dylanjacobsun/flight_Controller/Components/10nF_Cap_0603.step

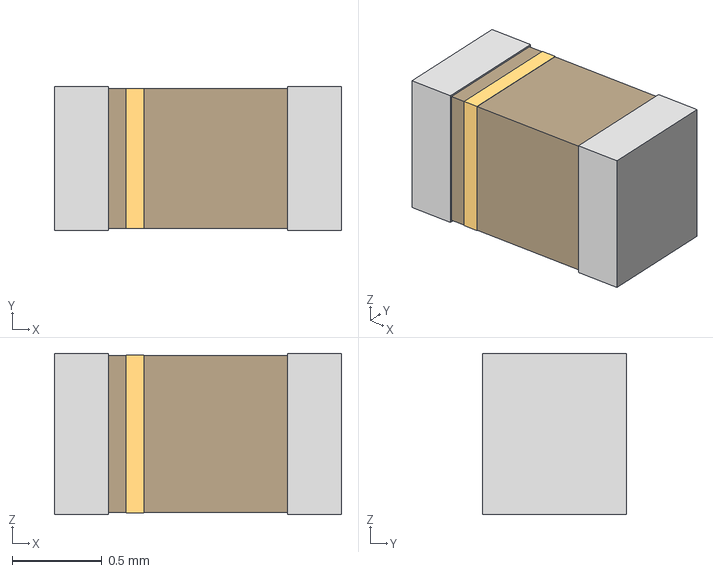
[picture p15: CAD file, 2025-04-18]
Components/10nF_Cap_0603.step
1.60 x 0.8 x 0.9 mm
