dylanjacobsun/flight_Controller/Components/33.2Resistor.step

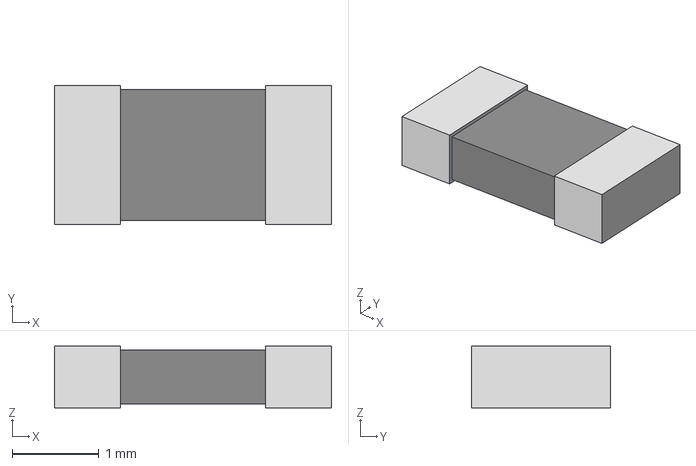
[picture p16: CAD file, 2025-04-17]
Components/33.2Resistor.step
3.20 x 1.60 x 0.711 mm
