dylanjacobsun/flight_Controller/Components/22Uf_CAP.step

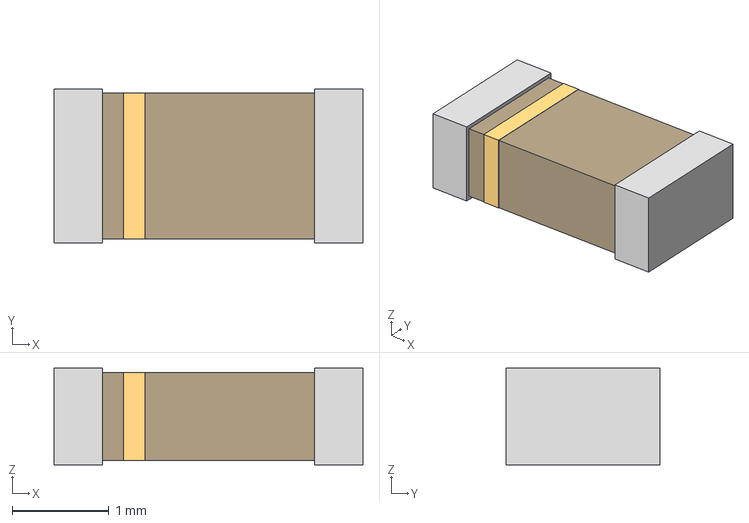
[picture p17: CAD file, 2025-04-17]
Components/22Uf_CAP.step
3.20 x 1.60 x 1.00 mm
