dylanjacobsun/flight_Controller/Components/3_3_Inductor.step

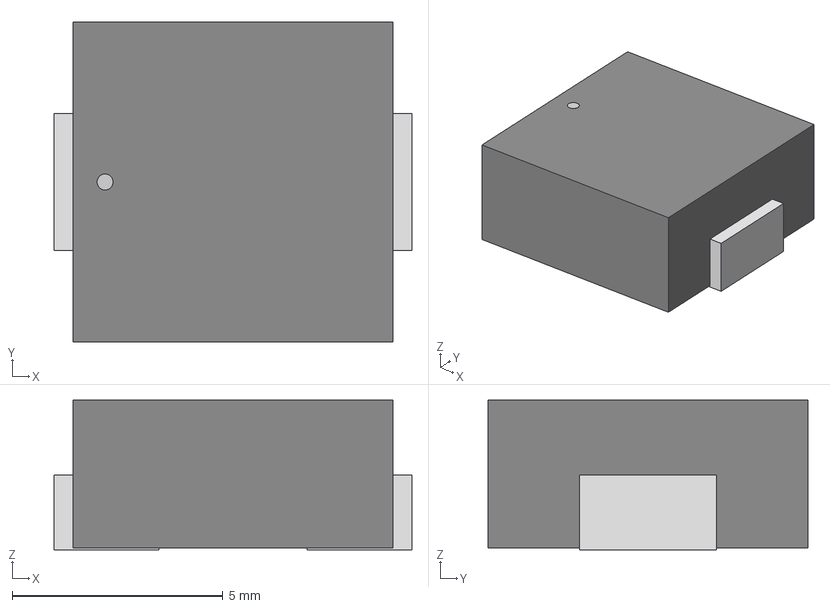
[picture p18: CAD file, 2025-04-17]
Components/3_3_Inductor.step
8.50 x 7.59 x 3.56 mm
