dylanjacobsun/flight_Controller/Components/STM32F446VET6.step

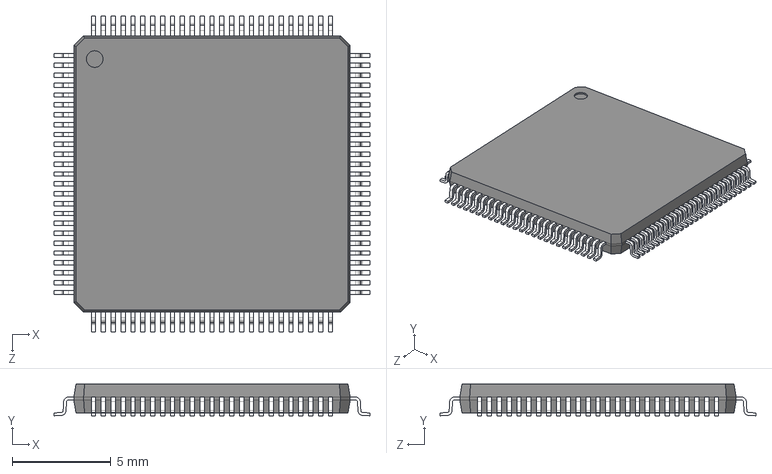
[picture p19: CAD file, 2025-04-16]
Components/STM32F446VET6.step
16.0 x 1.60 x 16.0 mm
