dylanjacobsun/flight_Controller/Components/DPS368XTSA1.step

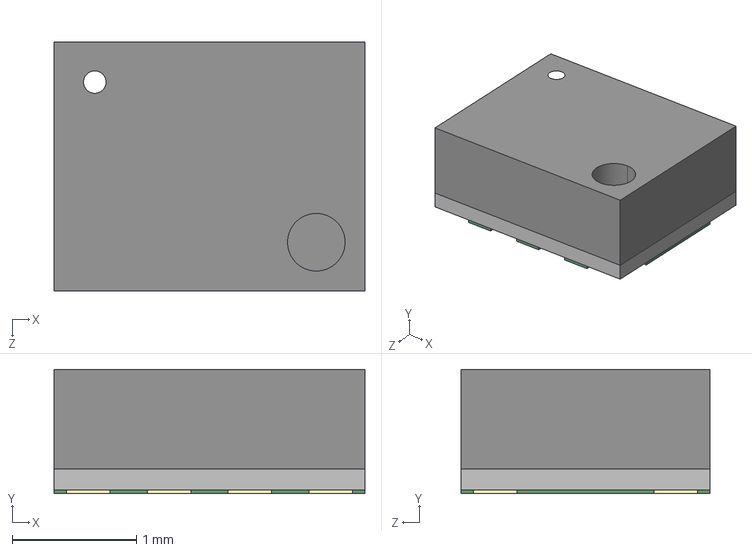
[picture p20: CAD file, 2025-04-16]
Components/DPS368XTSA1.step
2.50 x 1.00 x 2.00 mm
