dylanjacobsun/flight_Controller/Components/0.22Cap.step

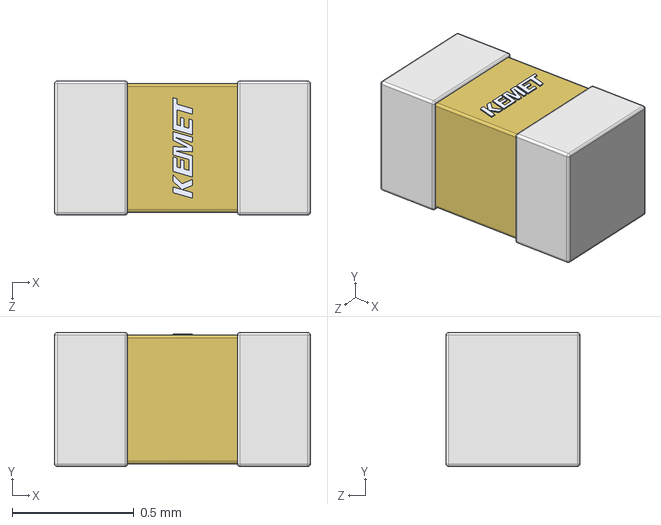
[picture p21: CAD file, 2025-04-16]
Components/0.22Cap.step
1.05 x 0.55 x 0.55 mm
