dylanjacobsun/flight_Controller/Components/ICM-42670-P.step

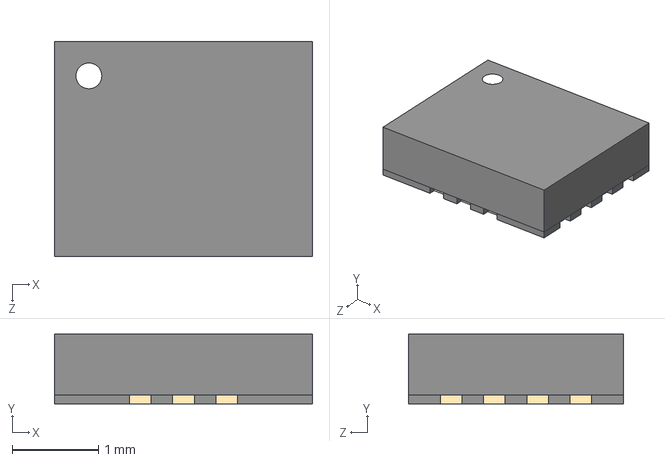
[picture p22: CAD file, 2025-04-16]
Components/ICM-42670-P.step
3.00 x 0.81 x 2.50 mm
