dylanjacobsun/flight_Controller/Components/U.FL-R-SMT_10_.step

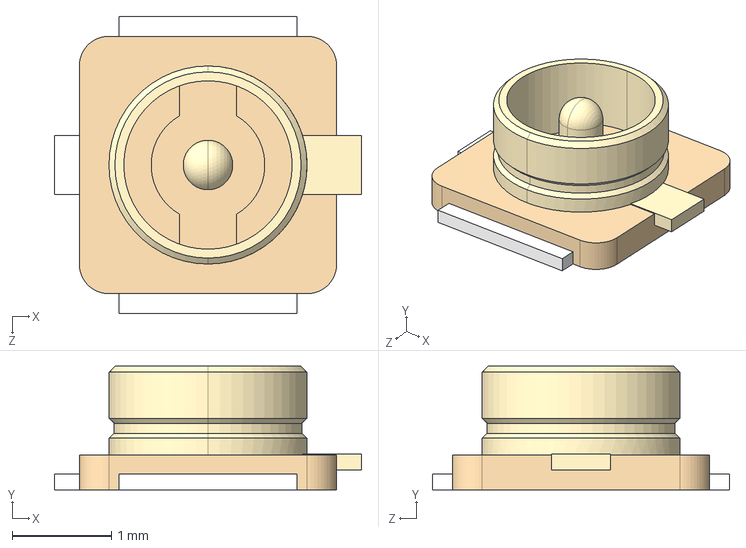
[picture p23: CAD file, 2025-04-16]
Components/U.FL-R-SMT_10_.step
3.10 x 1.25 x 3.00 mm
