dylanjacobsun/flight_Controller/Components/usbc.stp

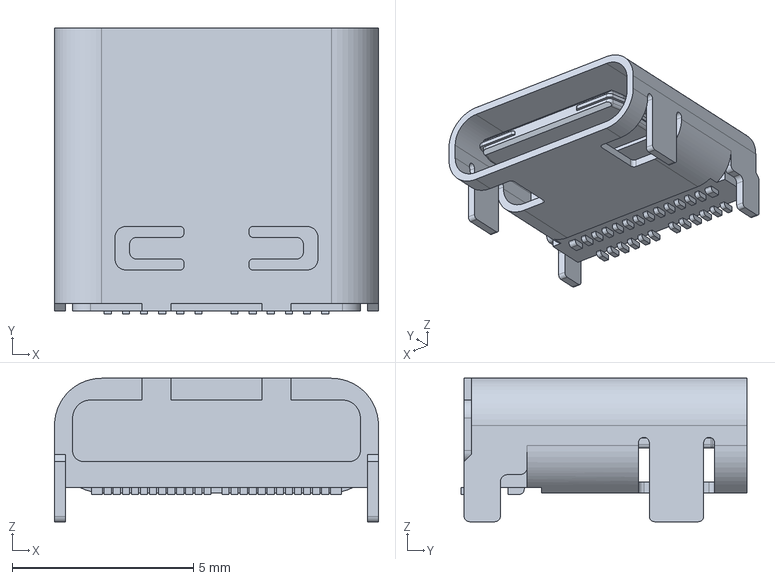
[picture p24: CAD file, 2025-04-16]
Components/usbc.stp
8.94 x 7.90 x 3.96 mm
