dylanjacobsun/flight_Controller/Components/3.3Buck.step

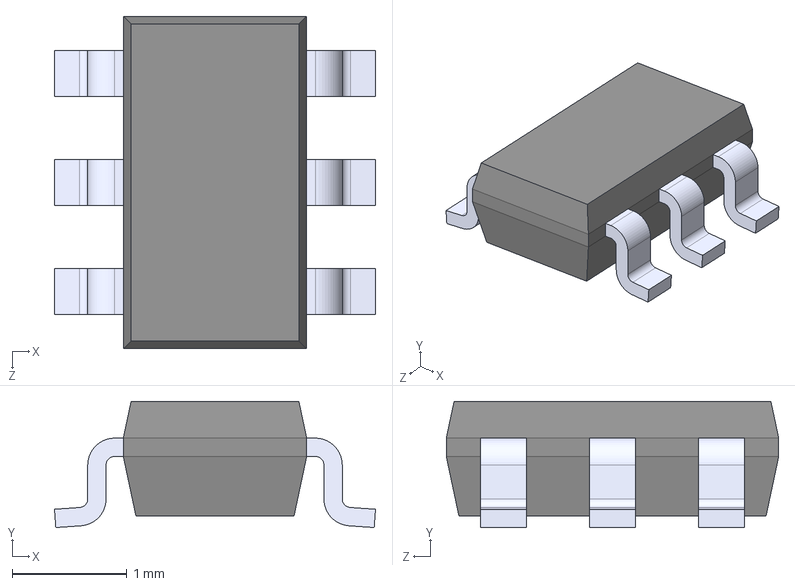
[picture p25: CAD file, 2025-04-16]
Components/3.3Buck.step
2.80 x 1.10 x 2.90 mm
