dylanjacobsun/flight_Controller/Components/Crystal.step

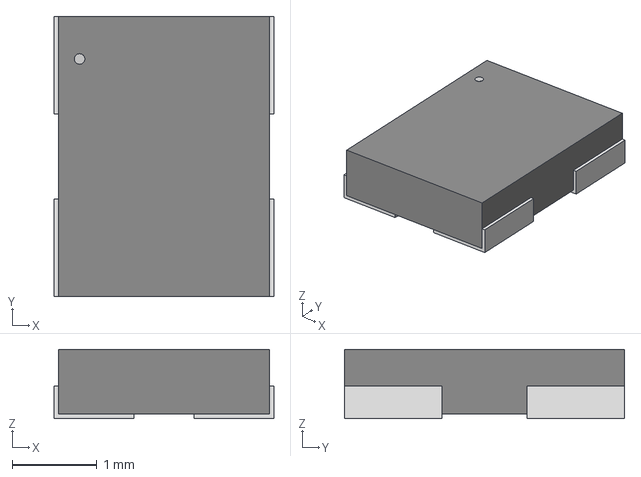
[picture p26: CAD file, 2025-04-16]
Components/Crystal.step
2.59 x 3.30 x 0.815 mm
