dylanjacobsun/flight_Controller/Components/TESEO-LIV3F.step

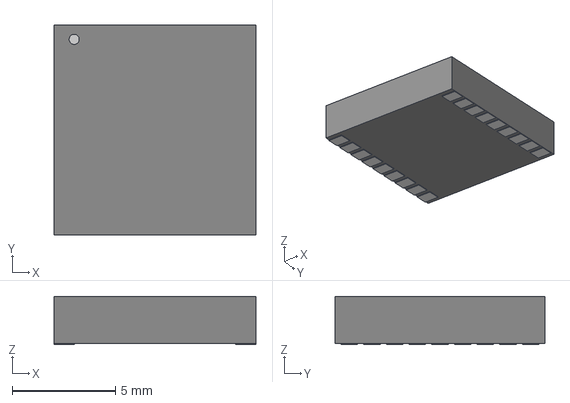
[picture p27: CAD file, 2025-04-16]
Components/TESEO-LIV3F.step
9.80 x 10.2 x 2.34 mm
